kierdavis/tape-punch-controller/firmware/src/TPC/LCDDriver.hpp

#ifndef __TPC_LCD_DRIVER_HPP
#define __TPC_LCD_DRIVER_HPP

#include <stdint.h>

#include <avr/pgmspace.h>

namespace TPC {
  namespace LCDDriver {
    void init();
    void setCursorPos(const uint8_t row, const uint8_t col);
    void writeData(const uint8_t data);
  }
}

#define LCD_WRITE_AT(ROW, COL, STR) { \
  static const char str[] PROGMEM = STR; \
  TPC::LCDDriver::writeAtP(ROW, COL, str); \
}

#endif
