kierdavis/tape-punch-controller/firmware/src/TPC/USBDriver.cpp

#include <stdbool.h>
#include <stdint.h>

#include <LUFA/Drivers/USB/USB.h>

#include "TPC/Log.hpp"
#include "TPC/Scheduler.hpp"
#include "TPC/SCSI.hpp"
#include "TPC/Timekeeping.hpp"
#include "TPC/USBDescriptor.hpp"
#include "TPC/USBDriver.hpp"

// Encapsulates runtime state of Mass Storage interface.
static USB_ClassInfo_MS_Device_t msdInfo = {
  .Config = {
    .InterfaceNumber = (uint8_t) TPC::USBDescriptor::InterfaceNumber::MASS_STORAGE,
    .DataINEndpoint = {
      .Address = (uint8_t) TPC::USBDescriptor::EndpointAddr::MASS_STORAGE_IN,
      .Size    = TPC::USBDescriptor::MASS_STORAGE_EPSIZE,
      .Type    = EP_TYPE_BULK,
      .Banks   = 1,
    },
    .DataOUTEndpoint = {
      .Address = (uint8_t) TPC::USBDescriptor::EndpointAddr::MASS_STORAGE_OUT,
      .Size    = TPC::USBDescriptor::MASS_STORAGE_EPSIZE,
      .Type    = EP_TYPE_BULK,
      .Banks   = 1,
    },
    .TotalLUNs = 1,
  },
};

static void scheduleTask() {
  TPC::Scheduler::schedule(
    TPC::Scheduler::TaskID::USB_DRIVER_SERVICE,
    TPC::Timekeeping::Interval::fromMilliseconds(1)
  );
}

void TPC::USBDriver::init() {
  // Initialise LUFA.
  USB_Init();

  scheduleTask();
}

void TPC::USBDriver::serviceTask() {
  scheduleTask();

  MS_Device_USBTask(&msdInfo);
  USB_USBTask();
}

// LUFA callbacks below.

extern "C" {
  void EVENT_USB_Device_Connect() {
    LOG(DEBUG, "[USB] enumerating");
  }

  void EVENT_USB_Device_Disconnect() {
    LOG(INFO, "[USB] disconnected");
  }

  void EVENT_USB_Device_ConfigurationChanged() {
    bool success = MS_Device_ConfigureEndpoints(&msdInfo);
    if (success) {
      LOG(INFO, "[USB] connected");
    } else {
      LOG(INFO, "[USB] configuration change failed");
    }
  }

  void EVENT_USB_Device_ControlRequest() {
    MS_Device_ProcessControlRequest(&msdInfo);
  }

  uint16_t CALLBACK_USB_GetDescriptor(uint16_t wValue,
                                      uint16_t wIndex,
                                      const void ** descriptorDest,
                                      uint8_t * memorySpaceDest) {
    uint8_t descriptorType = wValue >> 8;
    uint8_t descriptorNumber = wValue & 0xFF;
    TPC::USBDescriptor::Ref ref;
    bool ok = TPC::USBDescriptor::lookup(descriptorType, descriptorNumber, wIndex, &ref);
    if (ok) {
      *descriptorDest = ref.pointer;
      *memorySpaceDest = ref.memorySpace;
      return ref.size;
    } else {
      return NO_DESCRIPTOR;
    }
  }

  bool CALLBACK_MS_Device_SCSICommandReceived(USB_ClassInfo_MS_Device_t * msdInfo) {
    return TPC::SCSI::handle(&msdInfo->State.CommandBlock);
  }
};
