kierdavis/tape-punch-controller/firmware/src/TPC/FileSelector.cpp

#include <stdint.h>

#include "TPC/Config.hpp"
#include "TPC/FileSelector.hpp"
#include "TPC/Filesystem.hpp"
#include "TPC/Log.hpp"
#include "TPC/Scheduler.hpp"

static TPC::Filesystem::DirectoryEntry * files[TPC::Config::MAX_NUM_FILES];
static uint8_t numFiles = 0;
static uint8_t selectedIndex = 0; // considered invalid when numFiles == 0.
static TPC::Filesystem::DirectoryEntry * previousSelection = nullptr;

static void expediteScan() {
  TPC::Scheduler::expedite(TPC::Scheduler::TaskID::SCAN_FILESYSTEM);
}

void TPC::FileSelector::reset() {
  previousSelection = selected();
  numFiles = 0;
  selectedIndex = 0;
}

void TPC::FileSelector::add(TPC::Filesystem::DirectoryEntry * file) {
  uint8_t _numFiles = numFiles;
  if (_numFiles < TPC::Config::MAX_NUM_FILES) {
    files[_numFiles] = file;
    if (file == previousSelection) {
      selectedIndex = _numFiles;
      previousSelection = nullptr;
      LOG(DEBUG_VERBOSE, "[FileSelector] restored selection ", file);
    }
    numFiles = _numFiles + 1;
  }
}

void TPC::FileSelector::selectNext() {
  expediteScan();
  uint8_t _numFiles = numFiles;
  if (_numFiles == 0) { return; }
  uint8_t _selectedIndex = selectedIndex;
  _selectedIndex++;
  if (_selectedIndex == _numFiles) {
    _selectedIndex = 0;
  }
  LOG(DEBUG, "[FileSelector] selected ", files[_selectedIndex]);
  selectedIndex = _selectedIndex;
}

void TPC::FileSelector::selectPrev() {
  expediteScan();
  uint8_t _numFiles = numFiles;
  if (_numFiles == 0) { return; }
  uint8_t _selectedIndex = selectedIndex;
  if (_selectedIndex == 0) {
    _selectedIndex = _numFiles;
  }
  _selectedIndex--;
  LOG(DEBUG, "[FileSelector] selected ", files[_selectedIndex]);
  selectedIndex = _selectedIndex;
}

TPC::Filesystem::DirectoryEntry * TPC::FileSelector::selected() {
  expediteScan();
  return (numFiles == 0) ? nullptr : files[selectedIndex];
}
