kierdavis/tape-punch-controller/firmware/src/TPC/Scheduler.hpp

#ifndef __TPC_SCHEDULER_HPP
#define __TPC_SCHEDULER_HPP

#include <stdint.h>

#include "TPC/Timekeeping.hpp"

namespace TPC {
  namespace Scheduler {
    enum class TaskID : uint8_t {
      LCD_STATUS_LINE_SCROLL,
      PRINTING_COMPLETE,
      SCAN_FILESYSTEM,
      TP_CONTROLLER_SERVICE,
      TP_DATA_PROVIDER_SERVICE,
      UI_BOTH_BUTTONS,
      UI_CANCEL_BUTTON,
      UI_CONFIRM_BUTTON,
      USB_DRIVER_SERVICE,
      _MAX = USB_DRIVER_SERVICE
    };
    static constexpr uint8_t NUM_TASKS = ((uint8_t) TaskID::_MAX) + 1;

    void init();
    void schedule(TaskID taskID, TPC::Timekeeping::Timestamp when);
    void schedule(TaskID taskID, TPC::Timekeeping::Interval delay);
    void schedule(TaskID taskID);
    void expedite(TaskID taskID);
    void cancel(TaskID taskID);
    void serviceTasks();
  }
}

#endif
