kierdavis/tape-punch-controller/firmware/src/TPC/UI.hpp

#ifndef __TPC_UI_HPP
#define __TPC_UI_HPP

namespace TPC {
  namespace UI {
    void init();
    void refresh_IE();
    void serviceTask_IE();
    void handleConfirmButton_IE();
    void handleCancelButton_IE();
    void handleBothButtons_IE();
  }
}

#endif
